Rosenberg60/RPT-Batteri/docs/waveshare_7_board_rev1.2.jpg

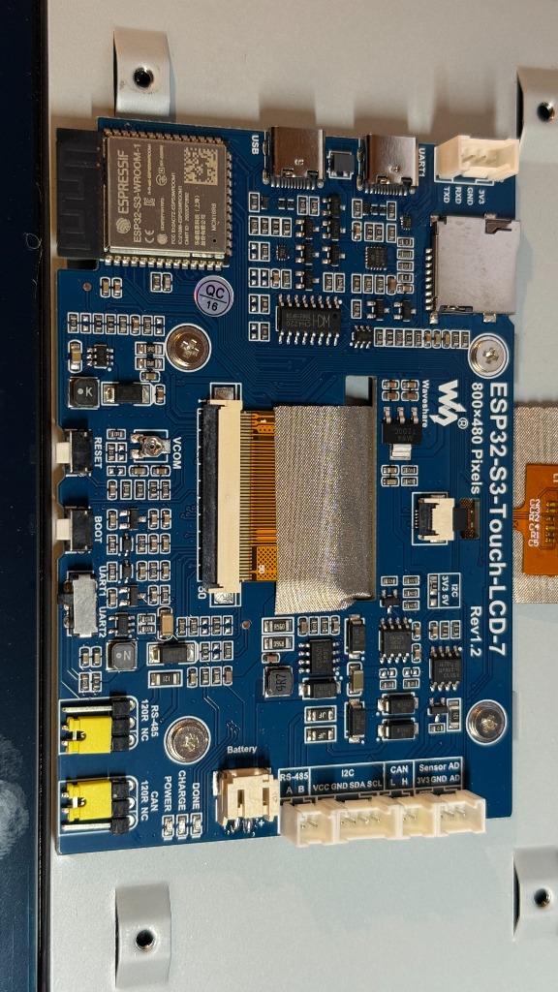
docs/waveshare_7_board_rev1.2.jpg
