Rosenberg60/RPT-Batteri/docs/crops/switch_zoom.jpg

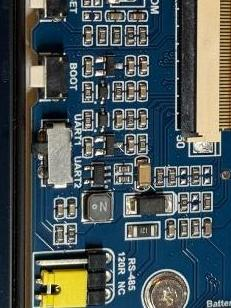
docs/crops/switch_zoom.jpg
