Rosenberg60/RPT-Batteri/docs/crops/board_connectors.jpg

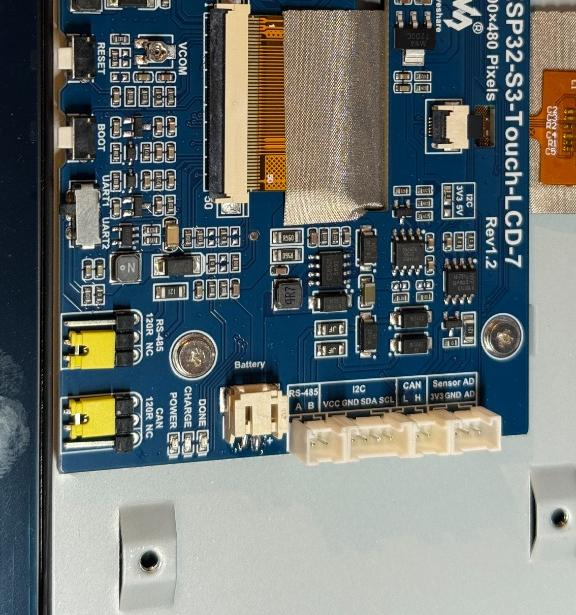
docs/crops/board_connectors.jpg
