Rosenberg60/RPT-Batteri/docs/switch_crop.jpg

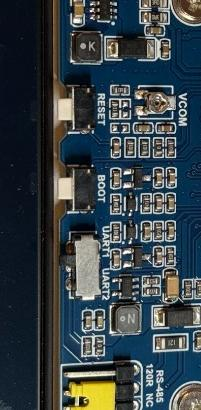
docs/switch_crop.jpg
