Rosenberg60/RPT-Batteri/3D_Print_Case/back_inside.png

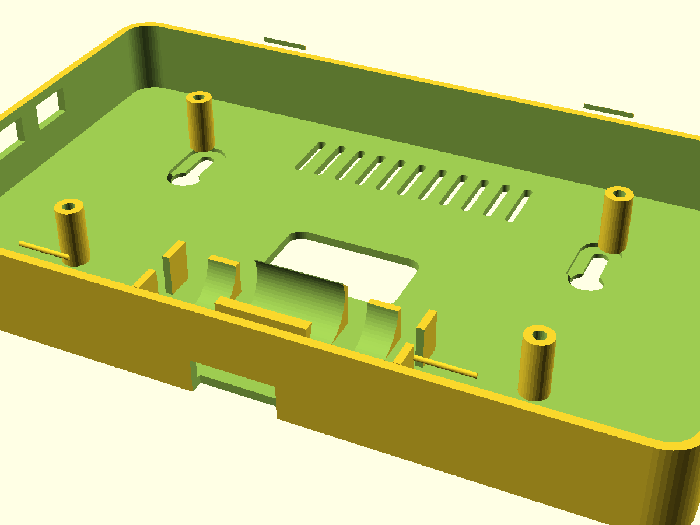
3D_Print_Case/back_inside.png
