Rosenberg60/RPT-Batteri/3D_Print_Case/back_inside_nostag.png

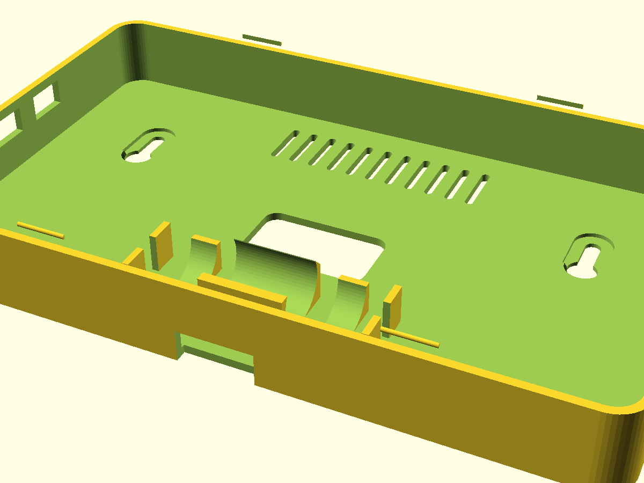
3D_Print_Case/back_inside_nostag.png
