Rosenberg60/RPT-Batteri/3D_Print_Case/back_view_full.png

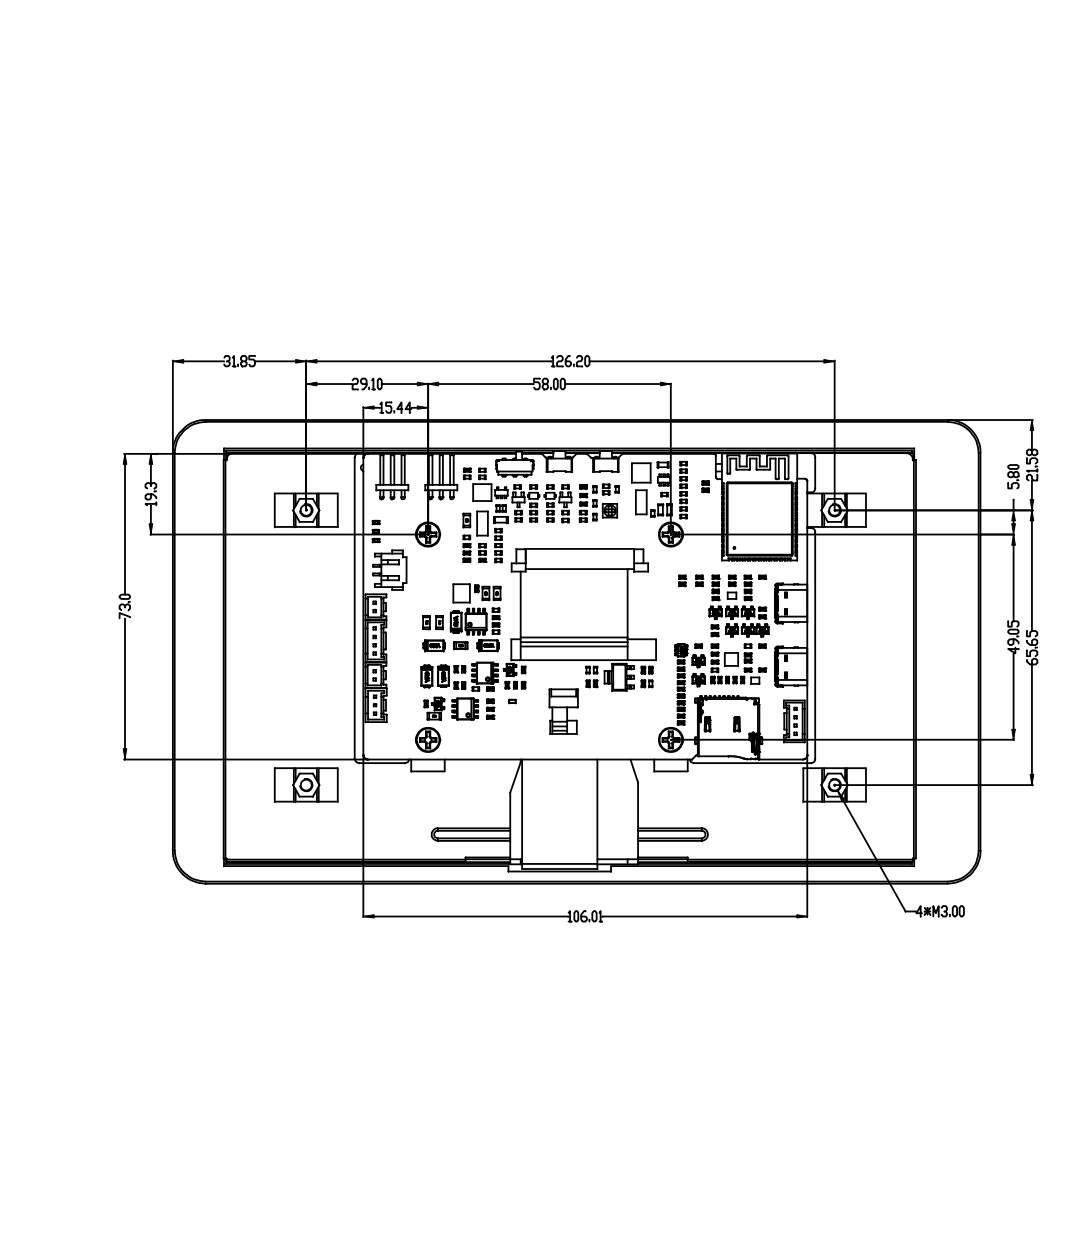
3D_Print_Case/back_view_full.png
