Rosenberg60/RPT-Batteri/3D_Print_Case/clamps_preview.png

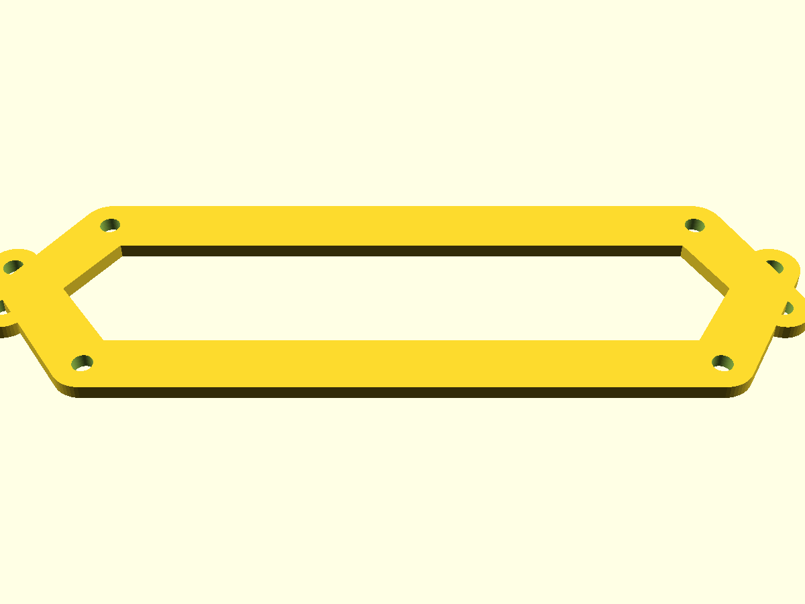
3D_Print_Case/clamps_preview.png
