Rosenberg60/RPT-Batteri/3D_Print_Case/enclosure_assembly_exploded.png

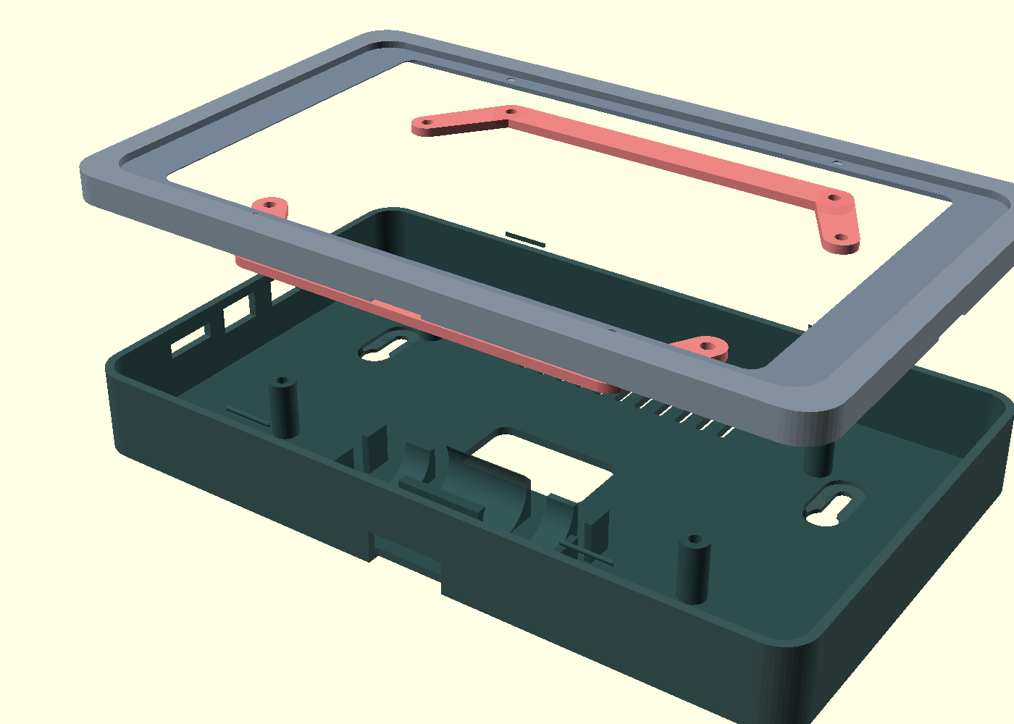
3D_Print_Case/enclosure_assembly_exploded.png
