Rosenberg60/RPT-Batteri/3D_Print_Case/enclosure_exploded_v3.png

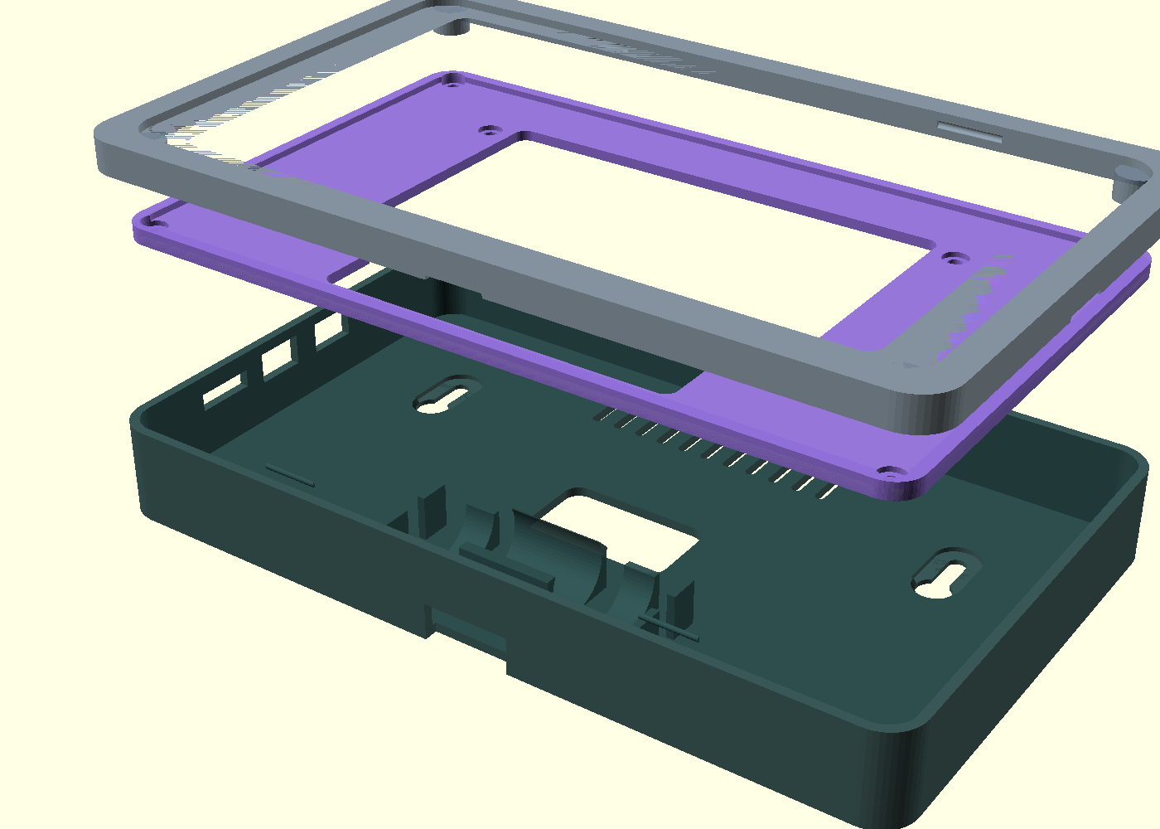
3D_Print_Case/enclosure_exploded_v3.png
