Rosenberg60/RPT-Batteri/3D_Print_Case/enclosure_preview.png

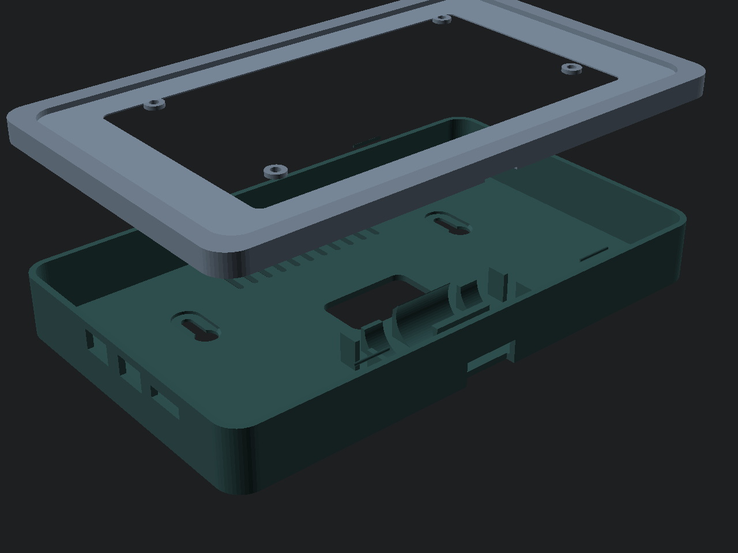
3D_Print_Case/enclosure_preview.png
