Rosenberg60/RPT-Batteri/3D_Print_Case/front_inside.png

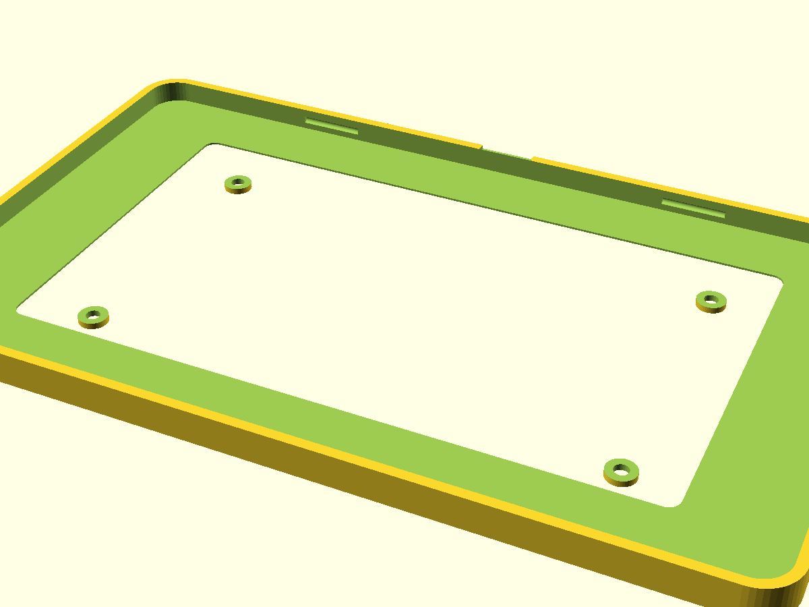
3D_Print_Case/front_inside.png
