Rosenberg60/RPT-Batteri/3D_Print_Case/front_inside_checked.png

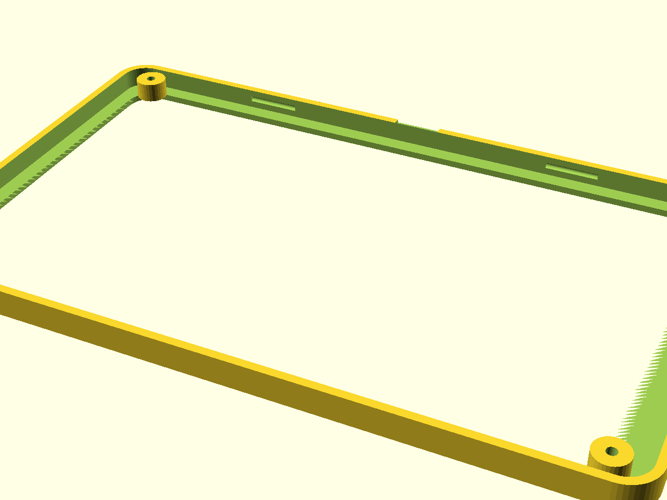
3D_Print_Case/front_inside_checked.png
