Rosenberg60/RPT-Batteri/3D_Print_Case/front_outside_view.png

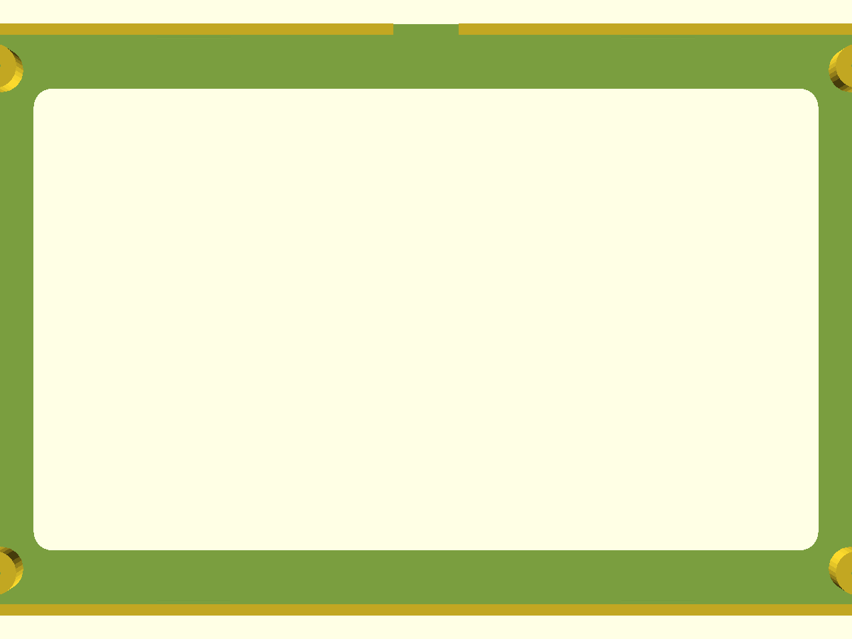
3D_Print_Case/front_outside_view.png
