Rosenberg60/RPT-Batteri/3D_Print_Case/front_view_crop.png

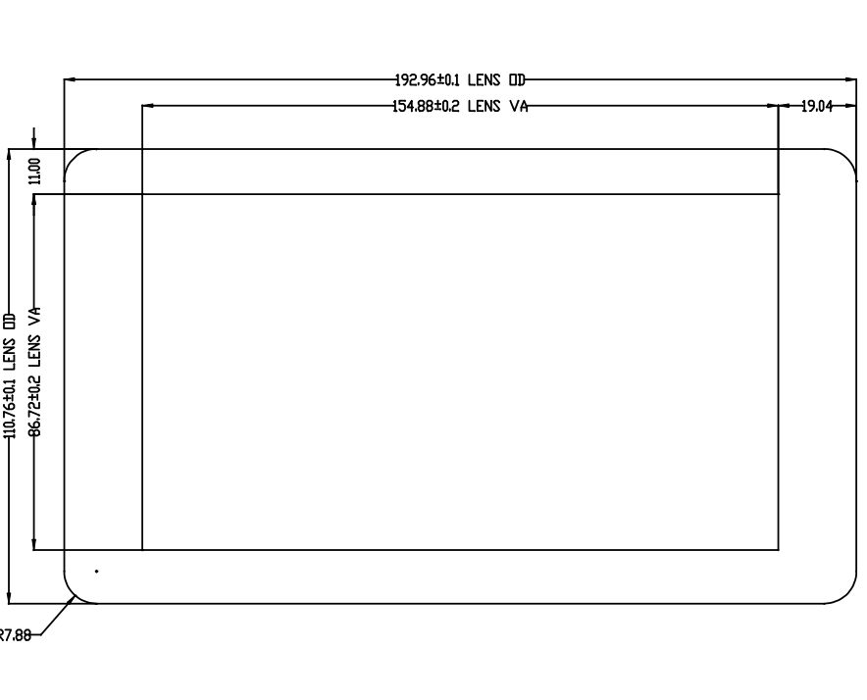
3D_Print_Case/front_view_crop.png
