Rosenberg60/RPT-Batteri/3D_Print_Case/front_view_up.png

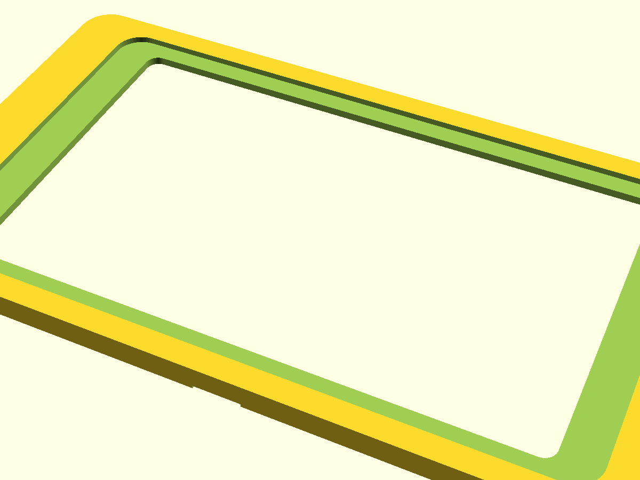
3D_Print_Case/front_view_up.png
