Rosenberg60/RPT-Batteri/3D_Print_Case/mellemstykke_preview.png

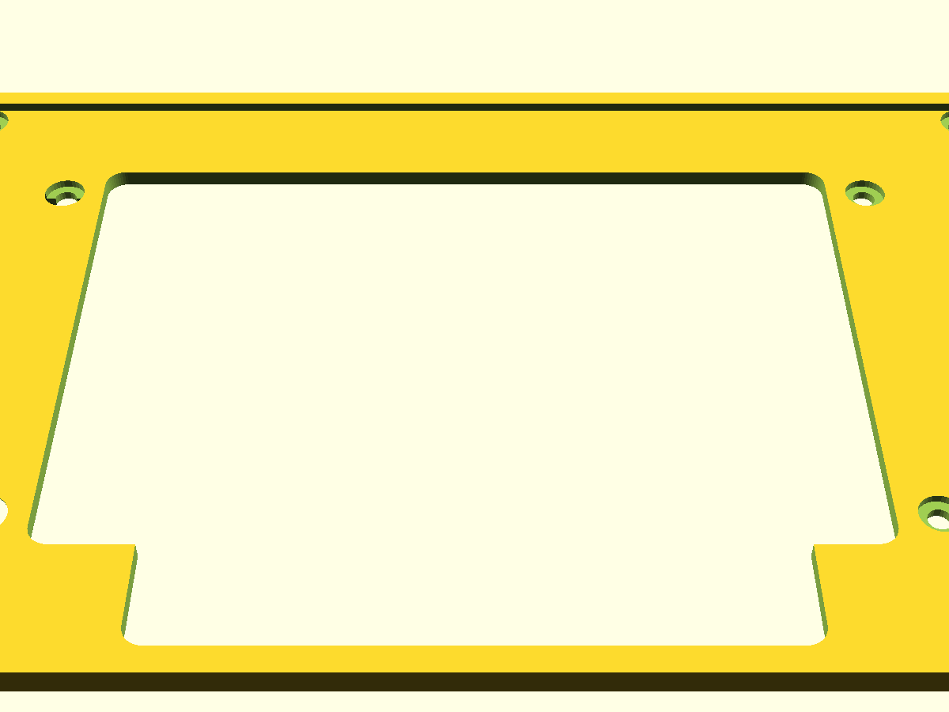
3D_Print_Case/mellemstykke_preview.png
