Rosenberg60/RPT-Batteri/3D_Print_Case/side_view_crop.png

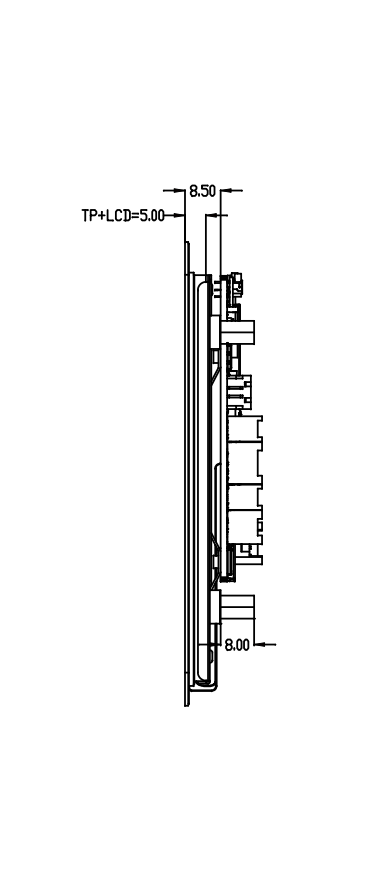
3D_Print_Case/side_view_crop.png
